bablokb/sensor-test/plots/aht20-absolute-int1.png

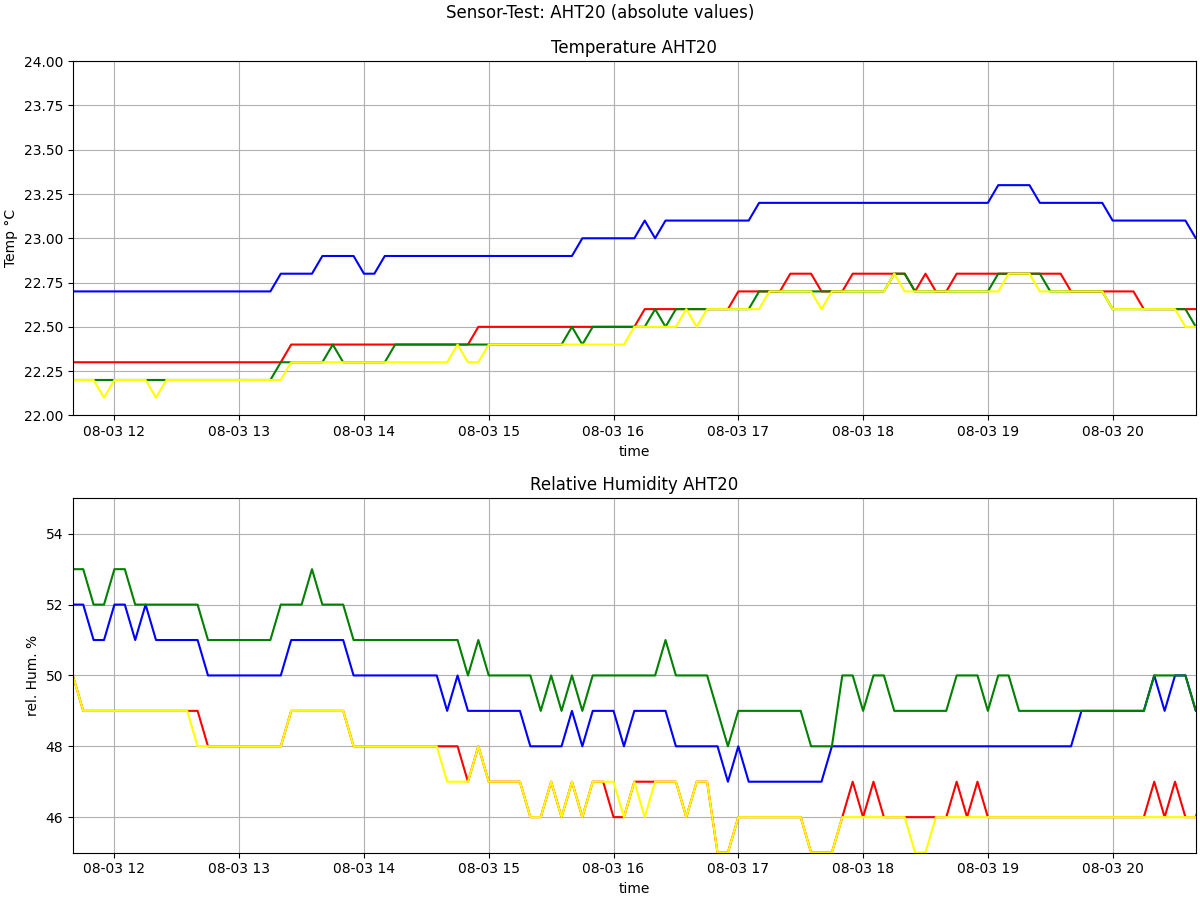
plots/aht20-absolute-int1.png
