bablokb/sensor-test/plots/aht20-absolute-int2.png

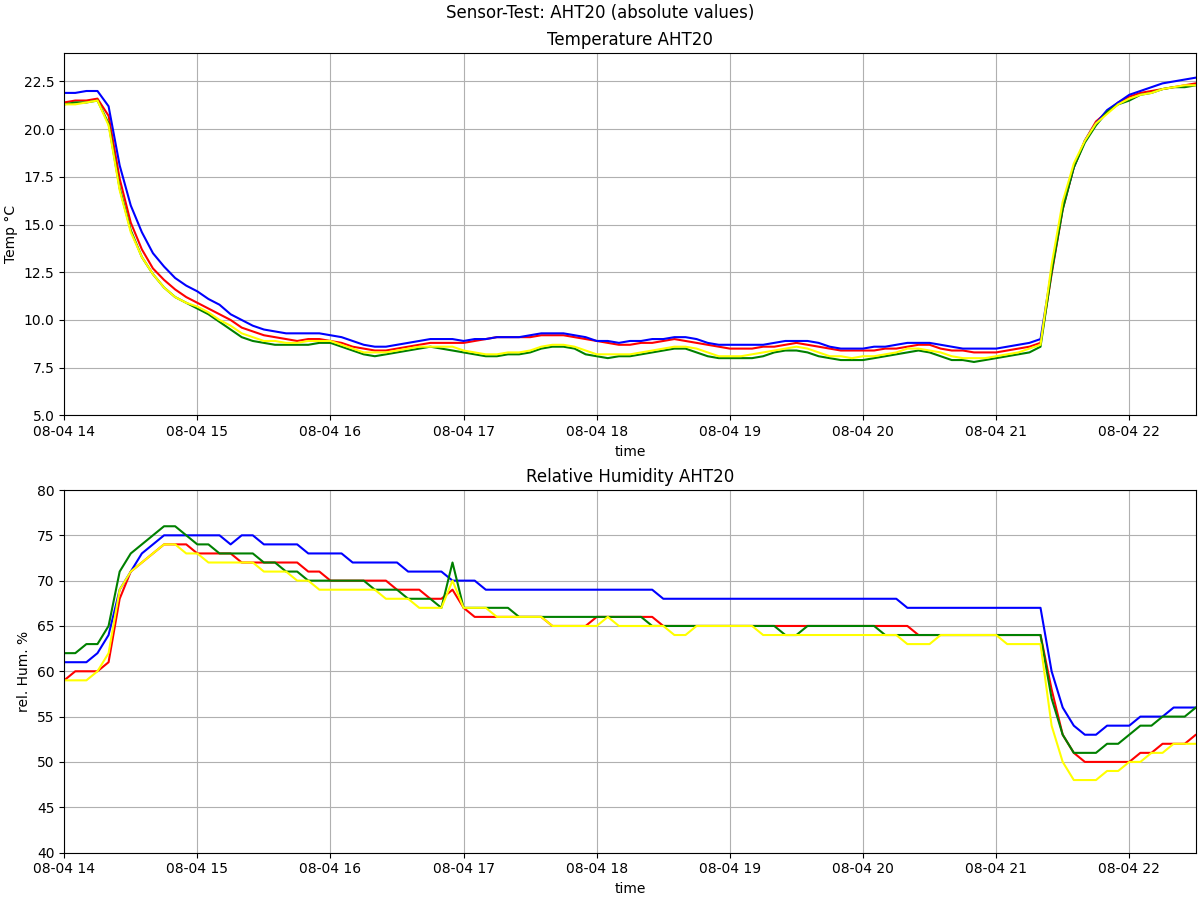
plots/aht20-absolute-int2.png
