bablokb/sensor-test/plots/all-hum-diff.png

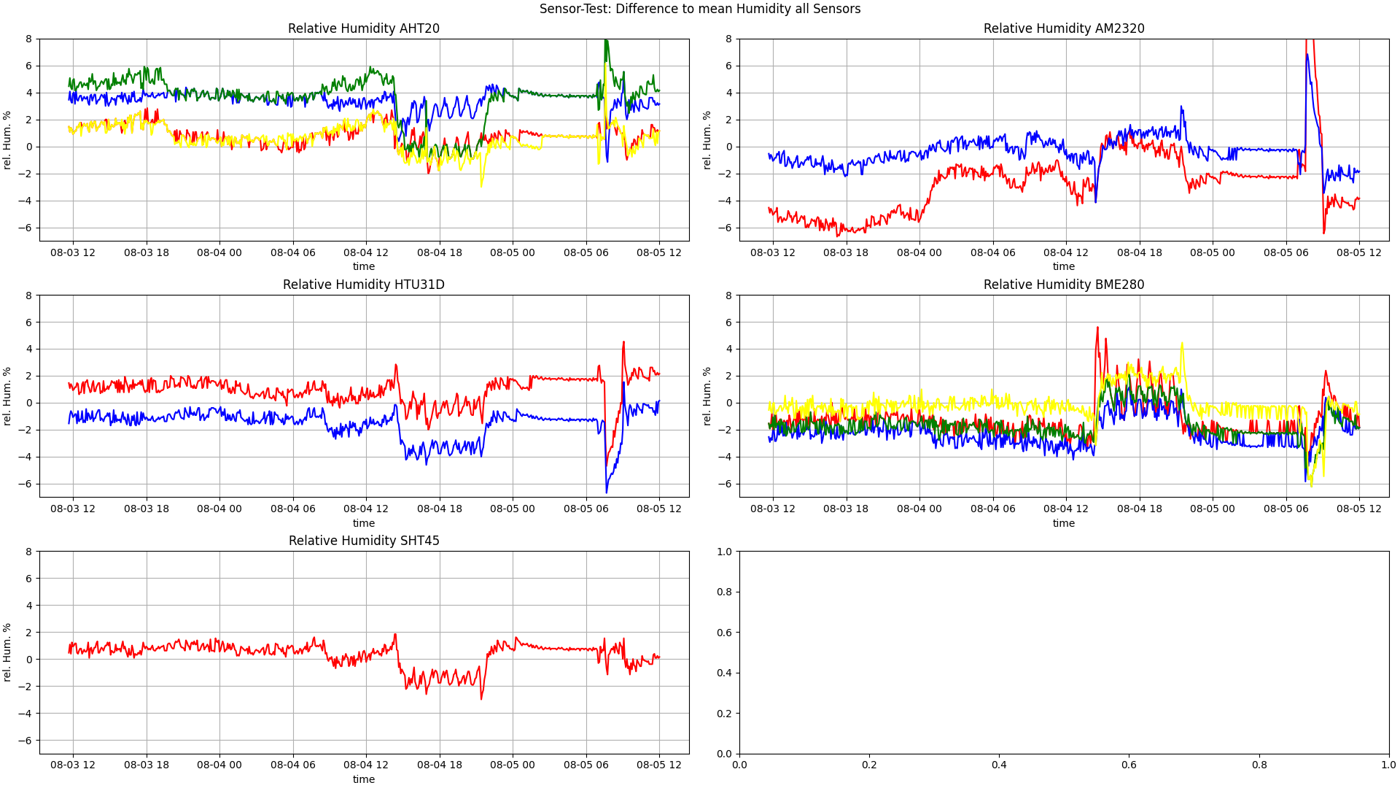
plots/all-hum-diff.png
