bablokb/sensor-test/plots/all-hum.png

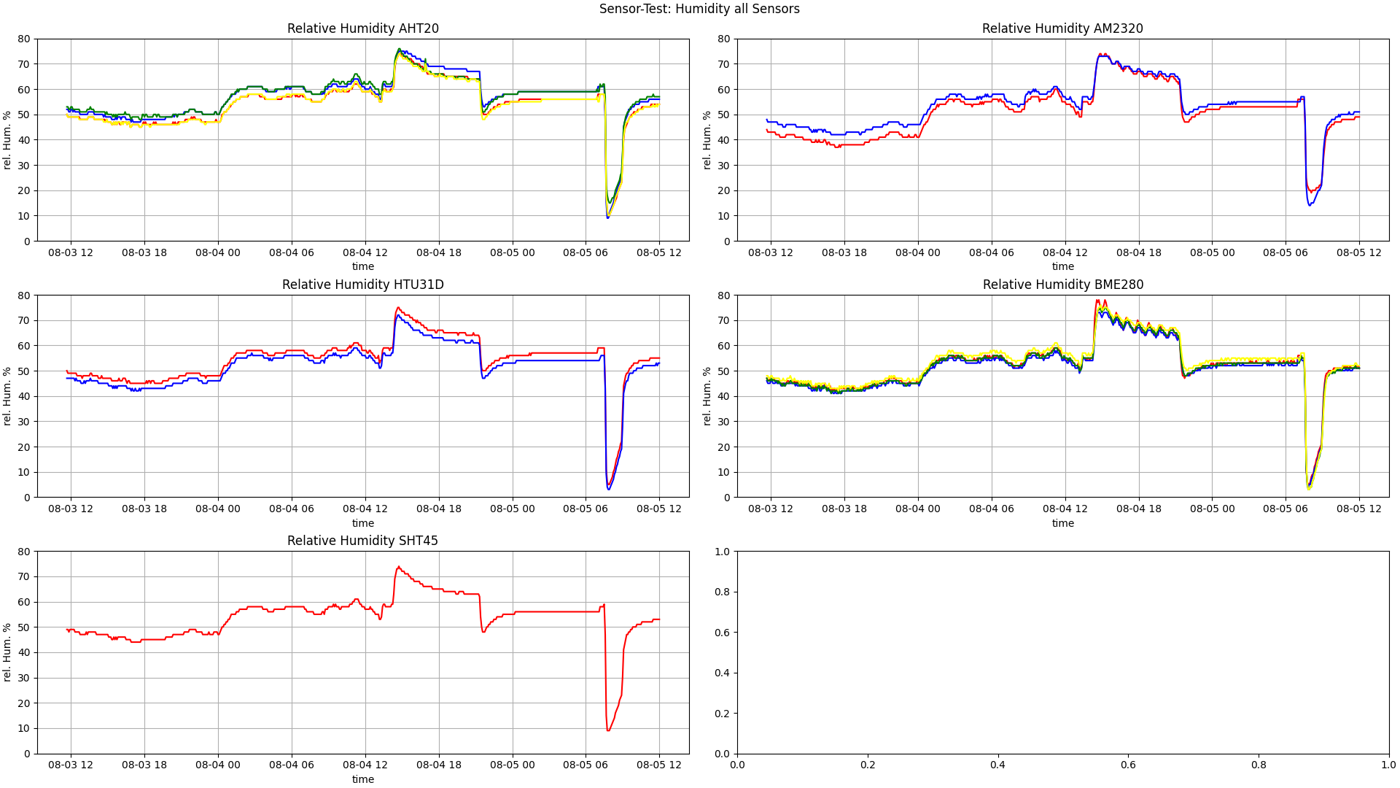
plots/all-hum.png
