bablokb/sensor-test/plots/all-press.png

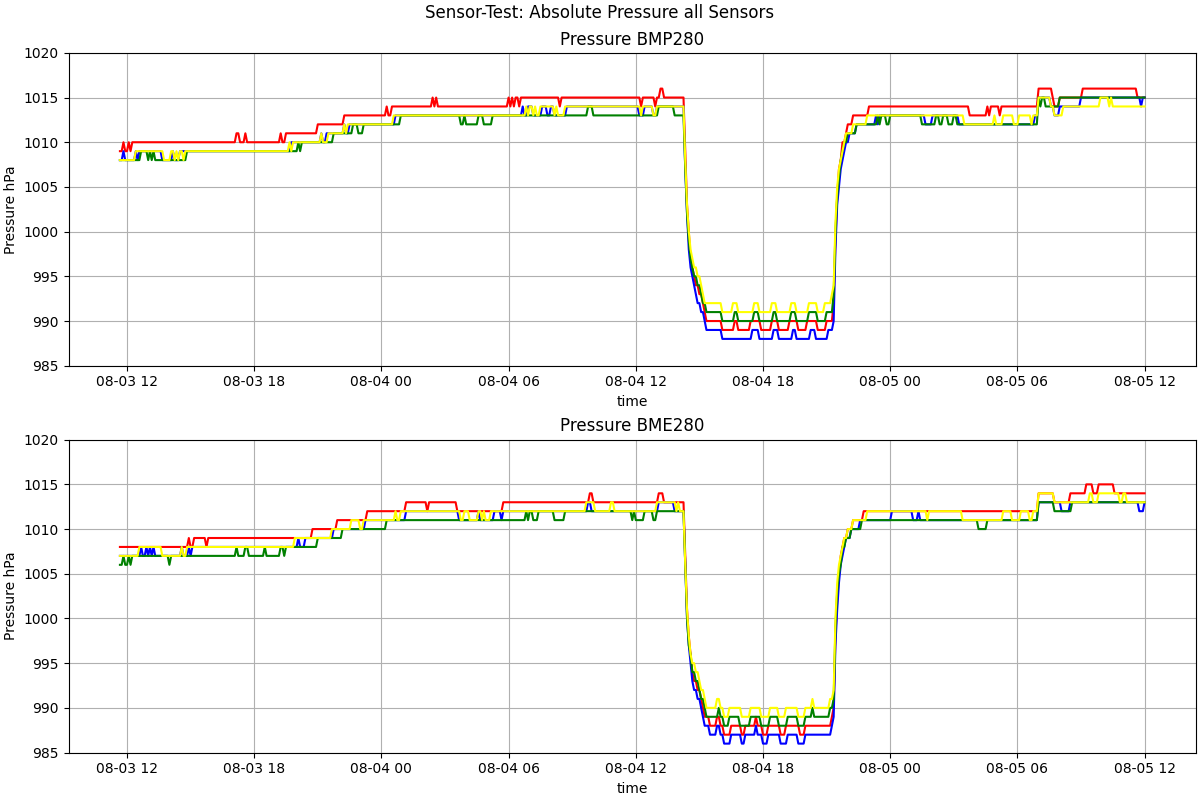
plots/all-press.png
