bablokb/sensor-test/plots/all-temp-diff.png

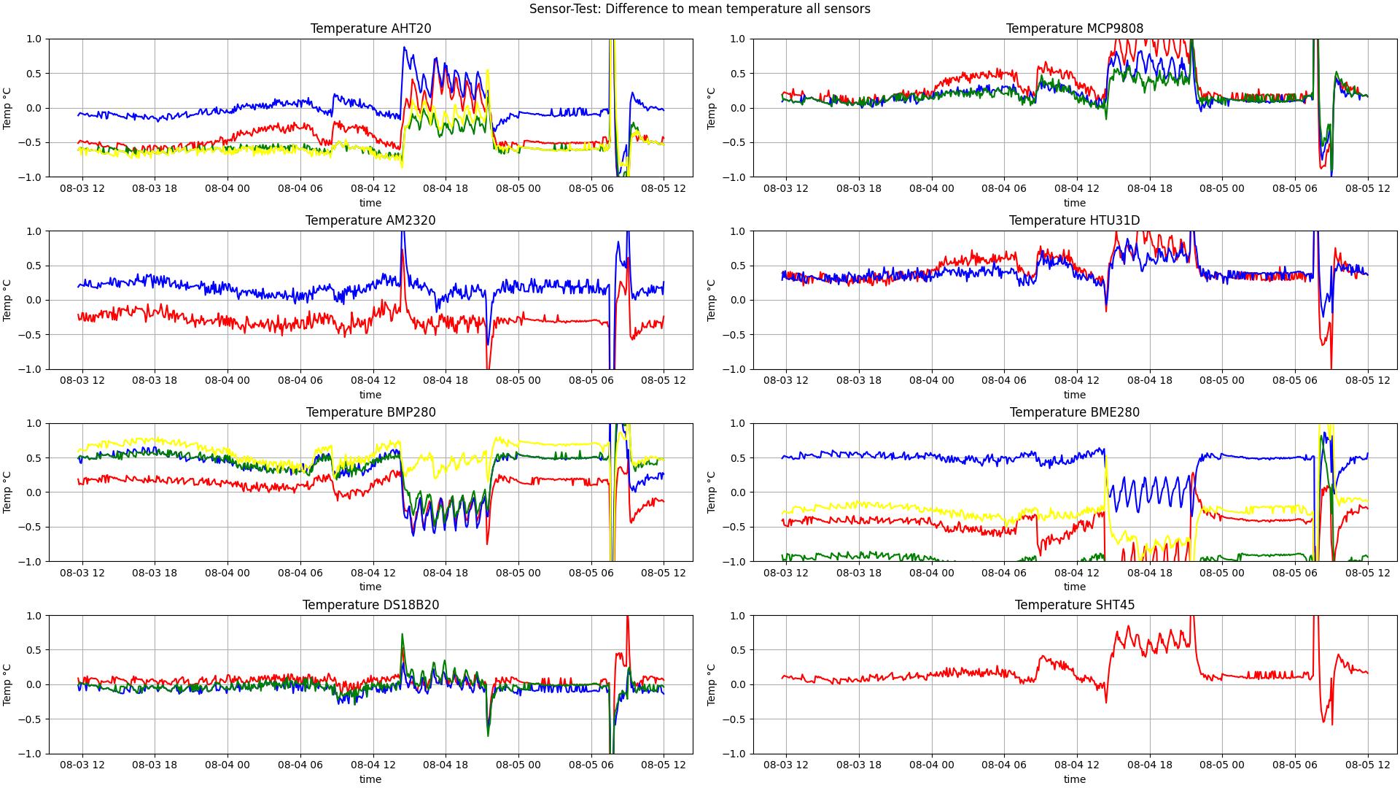
plots/all-temp-diff.png
