bablokb/sensor-test/plots/all-temp.png

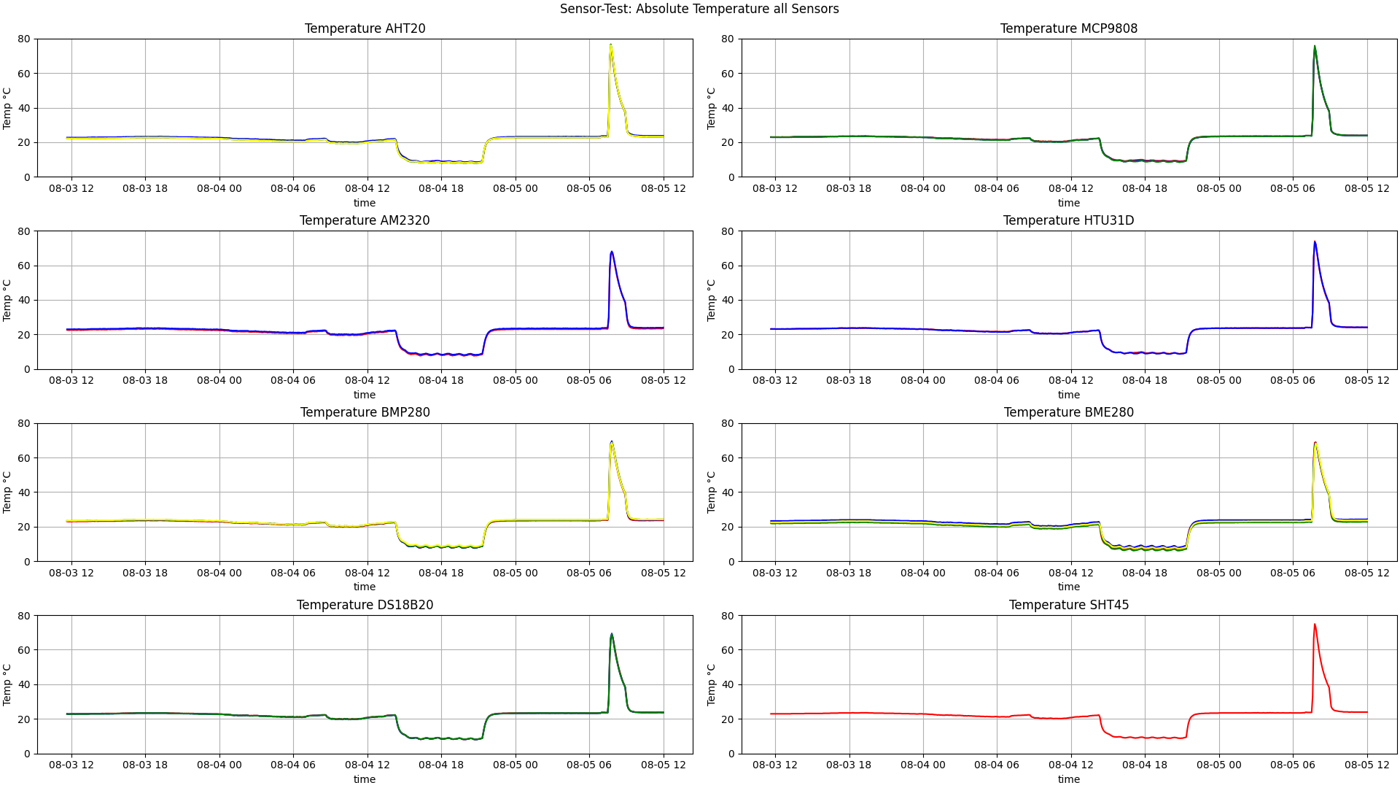
plots/all-temp.png
