bablokb/sensor-test/plots/bme280-absolute-int1.png

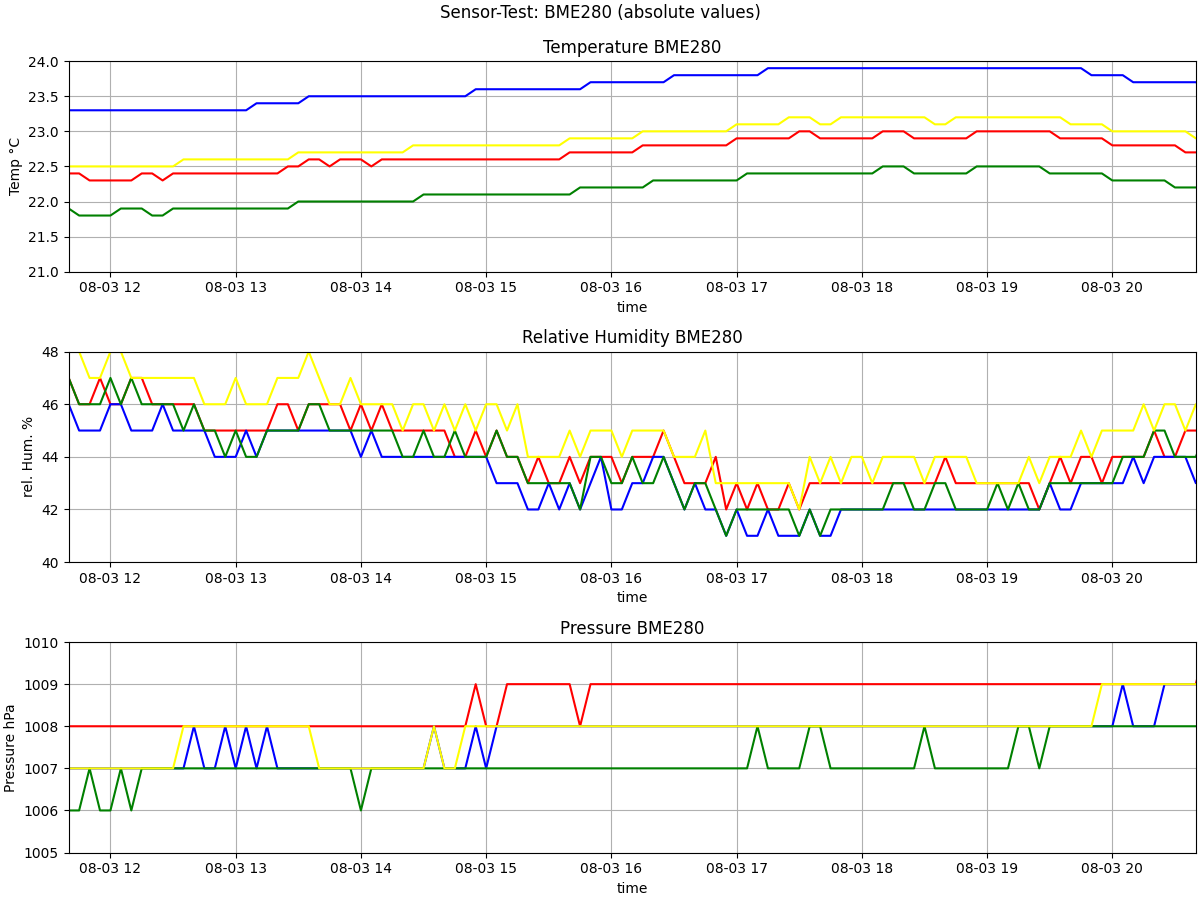
plots/bme280-absolute-int1.png
