bablokb/sensor-test/plots/bme280-absolute-int2.png

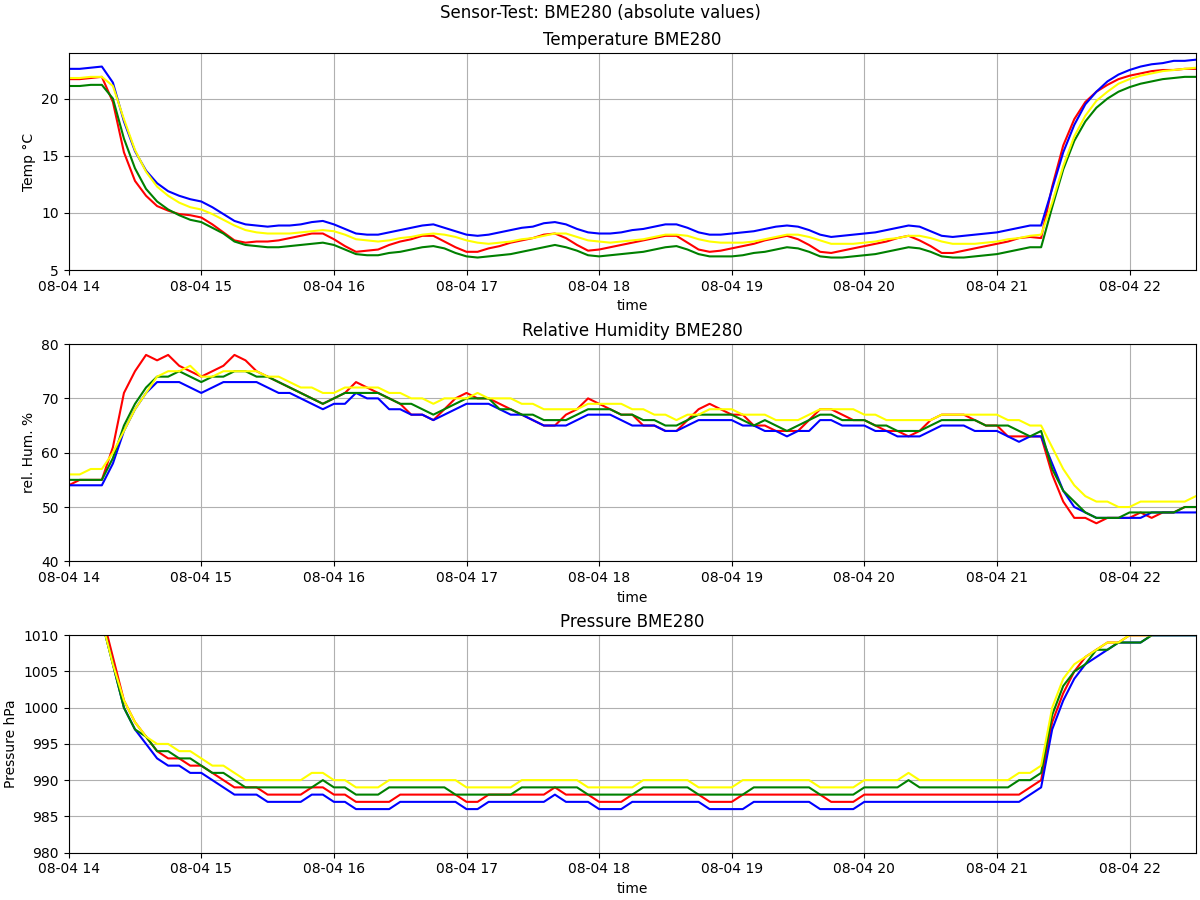
plots/bme280-absolute-int2.png
