bablokb/sensor-test/plots/ds18b20-absolute-int1.png

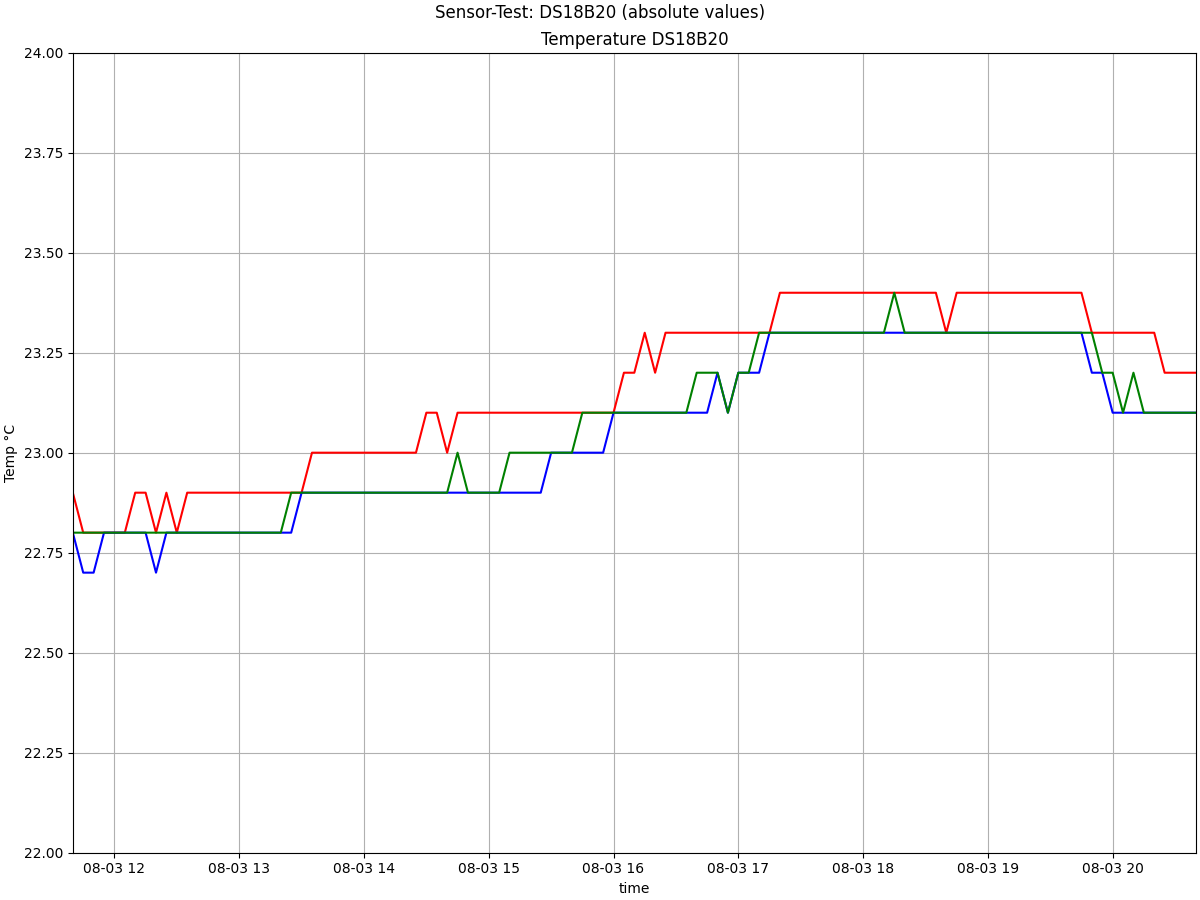
plots/ds18b20-absolute-int1.png
