bablokb/sensor-test/plots/ds18b20-absolute-int2.png

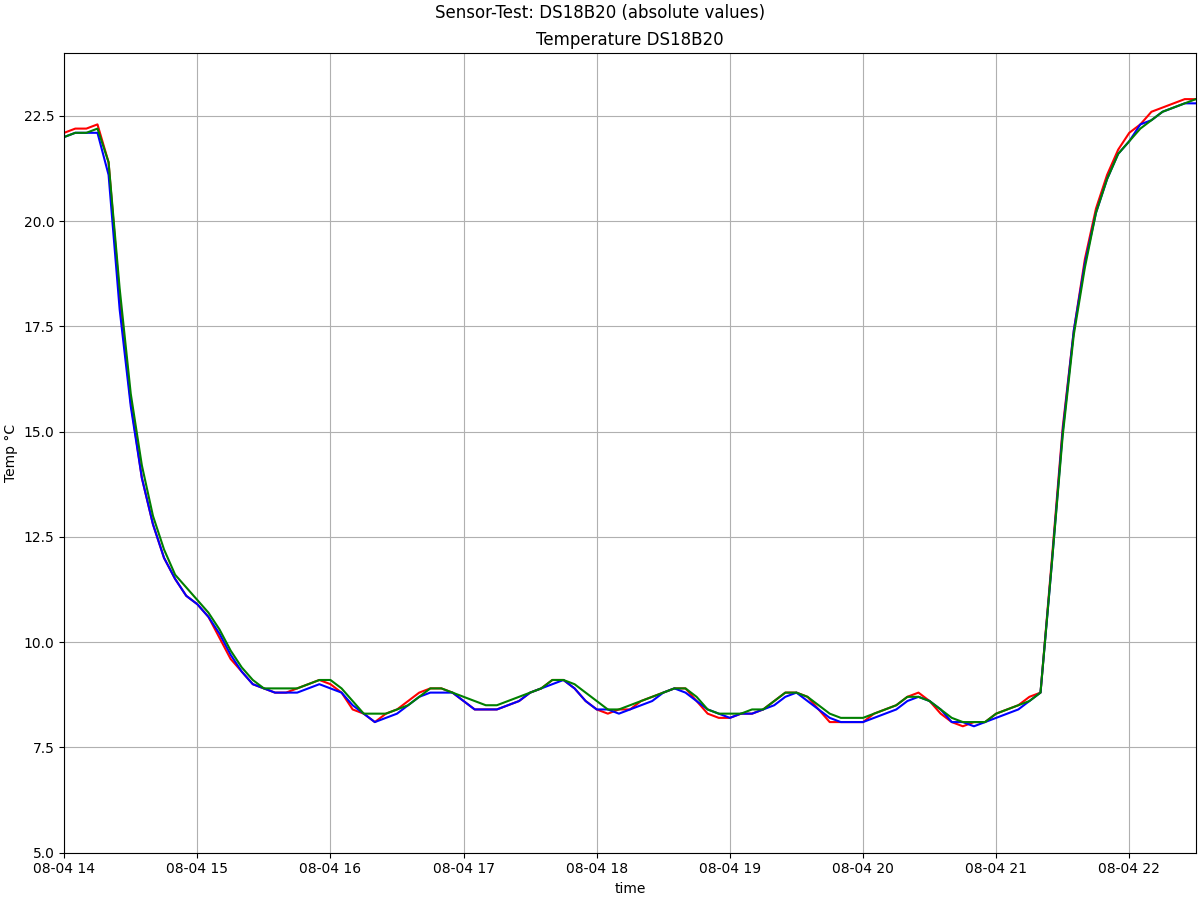
plots/ds18b20-absolute-int2.png
