bablokb/sensor-test/data/sensor-test1-ST2-raw.csv

#ID: ST2
#Location: 56JR+G5 FFB
#ts | Bat V | T/AHT °C | H/AHT %rH | T/MCP °C | T/AM °C | H/AM %rH | T/BMP °C | P/BMP | T/BME °C | H/BME %rH | P/BME | T/AHT °C | H/AHT %rH | T/SHT °C | H/SHT %rH | T/HTU °C | H/HTU %rH | T/BMP °C | P/BMP | T/BME °C | H/BME %rH | P/BME
2023-08-03T11:38:48 | 2.57 | 22.2 | 53 | 22.9 | 23.1 | 48 | 23.3 | 1008 | 21.8 | 47 | 1006 | 22.2 | 50 | 22.9 | 49 | 23.0 | 48 | 23.4 | 1008 | 22.5 | 48 | 1007
2023-08-03T11:40:06 | 2.60 | 22.2 | 53 | 23.0 | 23.0 | 48 | 23.3 | 1008 | 21.9 | 47 | 1006 | 22.2 | 50 | 22.9 | 49 | 23.1 | 47 | 23.4 | 1008 | 22.5 | 48 | 1007
2023-08-03T11:45:06 | 2.68 | 22.2 | 53 | 22.9 | 23.0 | 47 | 23.3 | 1008 | 21.8 | 46 | 1006 | 22.2 | 49 | 22.9 | 49 | 23.2 | 47 | 23.4 | 1008 | 22.5 | 48 | 1007
2023-08-03T11:50:06 | 2.60 | 22.2 | 52 | 22.9 | 23.0 | 47 | 23.3 | 1008 | 21.8 | 46 | 1007 | 22.2 | 49 | 22.9 | 48 | 23.1 | 47 | 23.4 | 1008 | 22.5 | 47 | 1007
2023-08-03T11:55:06 | 2.71 | 22.2 | 52 | 22.9 | 23.0 | 47 | 23.3 | 1008 | 21.8 | 46 | 1006 | 22.1 | 49 | 22.9 | 49 | 23.2 | 47 | 23.4 | 1008 | 22.5 | 47 | 1007
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
