bablokb/sensor-test/data/sensor-test1-diff.csv

2023-08-03T11:40:00 | 2.77 | -0.5130434782608724 | 1.46153846153846 | 0.1869565217391269 | 0.3869565217391262 | 1.46153846153846 | 0.1869565217391269 | 1.375 | -0.4130434782608745 | -1.53846153846154 | 0.375 | 0.08695652173912549 | -0.013043478260872376 | -0.013043478260872376 | -0.1130434782608738 | 3.46153846153846 | 0.08695652173912549 | -0.21304347826087167 | -4.53846153846154 | 0.4869565217391276 | 0.375 | 0.4869565217391276 | -2.53846153846154 | -0.625 | 2.6 | -0.6130434782608738 | 4.46153846153846 | 0.1869565217391269 | 0.1869565217391269 | -0.5384615384615401 | 0.4869565217391276 | 0.375 | -0.9130434782608745 | -1.53846153846154 | -1.625 | -0.6130434782608738 | 1.46153846153846 | 0.08695652173912549 | 0.4615384615384599 | 0.28695652173912833 | -1.53846153846154 | 0.5869565217391255 | 0.375 | -0.3130434782608731 | -0.5384615384615401 | -0.625
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
